olekgr/HP-35_Z80/photos/1_25.jpg

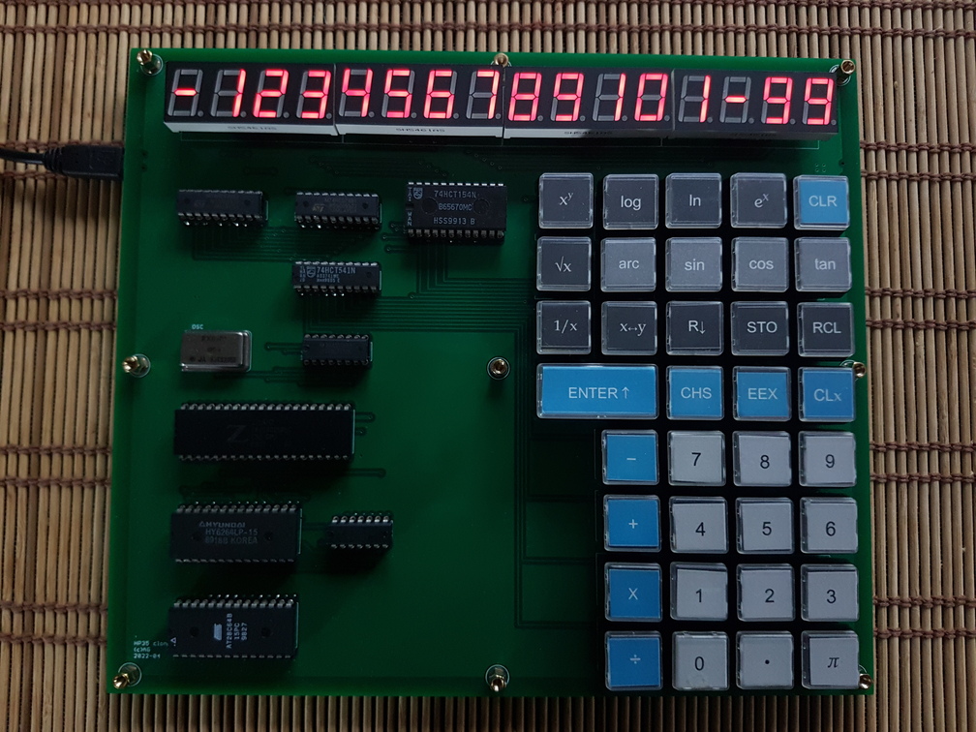
photos/1_25.jpg
